kenbarbour/meshtastic-rak19003-mini-case/scad/parts/frame-5050.scad

use <../case-frame.scad>;

width=50;
length=50;
thickness=10;
$fn=32;

case_frame(
	length=length,
	width=width,
	thickness=thickness
);
