kenbarbour/meshtastic-rak19003-mini-case/scad/parts/frame-5060.scad

use <../case-frame.scad>;

width=50;
length=60;
thickness=10;
$fn=32;

case_frame(
	length=length,
	width=width,
	thickness=thickness
);
